xtrinch/esp32s2-bme280-webusb/src/common.cpp

#include "common.h"
#include "driver/rtc_io.h"
#include "esp_adc_cal.h"

void ardprintf(const char *fmt, ...) {
  #if DEBUG != 1
  return;
  #endif

  int maxLen = 256;

  char buf[maxLen]; // resulting string limited to 128 chars
  buf[maxLen-1] = '\0';
  va_list args;
  va_start(args, fmt);
  vsnprintf(buf, 128, fmt, args);
  va_end(args);
  USBSerial.println(buf);
  Serial.println(buf);
}


void goToSleep(int secondsToSleep, bool forever = false) {
  ardprintf("Sleep: Every %d sec", secondsToSleep);

  Serial.flush();

  if (!forever) {
    esp_sleep_enable_timer_wakeup(secondsToSleep * uS_TO_S_FACTOR);
  }

  // does not work, input does not go high enough
  // always use power pin as a wakeup source
  // gpio_pullup_en((gpio_num_t)PWR_SENS_PIN);
  // esp_sleep_enable_ext0_wakeup((gpio_num_t)PWR_SENS_PIN, 1);

  // disables the brownout, apparently :)
  CLEAR_PERI_REG_MASK(RTC_CNTL_BROWN_OUT_REG, RTC_CNTL_BROWN_OUT_RST_ENA);
  esp_wifi_stop();
  esp_deep_sleep_start();
  ardprintf("This will never be printed");
}

int makeSecureNetworkRequest(const char * url, const char * authorization, const char * content, const char * response, const char * method, const char * certificate) {
  WiFiClientSecure client;
  if (certificate) {
    client.setCACert((const char *)certificate);
  }

  client.connect(url, 443);
  HTTPClient http;

  http.begin(client, url);

  http.addHeader("Content-Type", "application/json");
  http.addHeader("Accept", "application/json");
  http.addHeader("Authorization", authorization);
  int httpResponseCode = -1;
  if (strcmp(method, "POST") == 0) {
    httpResponseCode = http.POST(content);
  } else {
    httpResponseCode = http.GET();
  }

  if (httpResponseCode > 0) {
    ardprintf("Station: HTTPS %d", httpResponseCode);
    const char * payload = http.getString().c_str();
    // ardprintf("%s", payload);
    if (response != NULL) {
      strcpy((char *)response, payload);
    }
    http.end();
  }
  else {
    http.end();
    ardprintf("Station: Error code: %d", httpResponseCode);
  }

  return httpResponseCode;
}

bool connectToWifi() {
  int wifiRetriesLeft = 100;

  preferences.begin("iotfreezer", true);
  String ssid = preferences.getString("ssid");
  String password = preferences.getString("password");
  preferences.end();

  WiFi.begin(ssid.c_str(), password.c_str());

  while (WiFi.status() != WL_CONNECTED && wifiRetriesLeft > 0) {
    delay(100);
    wifiRetriesLeft -= 1;
  }

  if (wifiRetriesLeft <= 0 || WiFi.status() != WL_CONNECTED) {
    ardprintf("Station: Could not connect to WiFi.");
    return false;
  }
  
  ardprintf("Station: Connected to WiFi");

  return true;
}

bool saveCfg(
  const char * ssid, 
  const char * password, 
  const char * sensorAccessToken,
  uint8_t timeBetweenMeasurements, // min
  uint8_t maxRtcRecords // how many records before they are sent to server
) {
  if (!ssid || strlen(ssid) == 0 || !password || strlen(password) == 0) {
    ardprintf("Need SSID & password to save config");
    return false;
  }
  
  ardprintf("Saving ssid: %s", ssid);
  ardprintf("Saving password: %s", password);
  ardprintf("Saving access_token: %s", sensorAccessToken);
  ardprintf("Saving time_between: %d", timeBetweenMeasurements);
  ardprintf("Saving max_rtc_records: %d", maxRtcRecords);

  bool retVal = true;

  preferences.begin("iotfreezer", false);

  if (
    !preferences.putString("ssid", ssid) ||
    !preferences.putString("password", password) ||
    !preferences.putString("access_token", sensorAccessToken) ||
    !preferences.putInt("time_between", timeBetweenMeasurements) ||
    !preferences.putInt("max_rtc_records", maxRtcRecords) ||
    !preferences.putBool("cfg_saved", true)
  ) {
    ardprintf("Could not save some config data to preferences");
    retVal = false;
  }

  preferences.end();

  return retVal;
}

bool isCfgSaved() {
  preferences.begin("iotfreezer", true);
  bool cfgSaved = preferences.getBool("cfg_saved");
  preferences.end();
  return cfgSaved;
}

void check_efuse(void) {
  if (esp_adc_cal_check_efuse(ESP_ADC_CAL_VAL_EFUSE_TP) == ESP_OK) {
    ardprintf("eFuse Two Point: Supported\n");
  } else {
    ardprintf("Cannot retrieve eFuse Two Point calibration values. Default calibration values will be used.\n");
  }
}

// Use this, when you want to route VREF to a GPIO to measure it with a multimeter
// make sure it's after the attenuation set call
void routeVRefToGPIO(adc_unit_t adc_unit, gpio_num_t gpio) {
  esp_err_t status = adc_vref_to_gpio(adc_unit, gpio);
  if (status == ESP_OK) {
    printf("v_ref routed to GPIO\n");
  } else {
    printf("failed to route v_ref\n");
  }
  // loop forever so we never sleep
  while(true);
}
