xtrinch/esp32s2-bme280-webusb/include/epaper-display.h

#ifndef IOT_DISPLAY_H_INCLUDED
#define IOT_DISPLAY_H_INCLUDED

#include "bme280.h"

void setupDisplay();
void draw(bme280record * record, bool connectedToPower, int sleepInMinutes);
void showPcConn();

#endif
